omriharel/deej/assets/community-builds/extra/dimitar-schematic.png

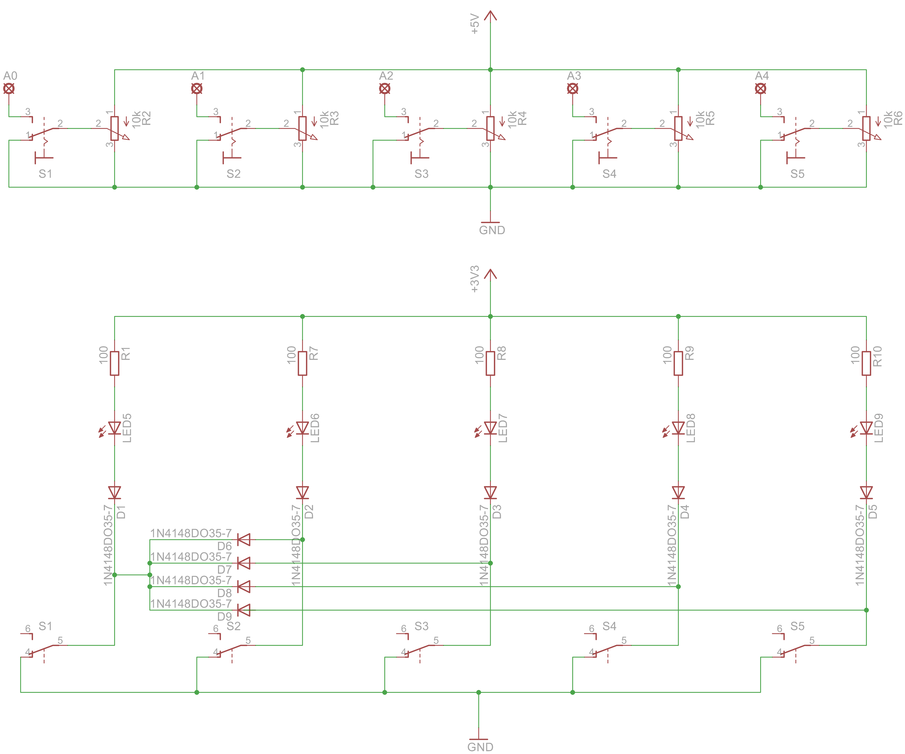
assets/community-builds/extra/dimitar-schematic.png
