omriharel/deej/assets/build-3d.png

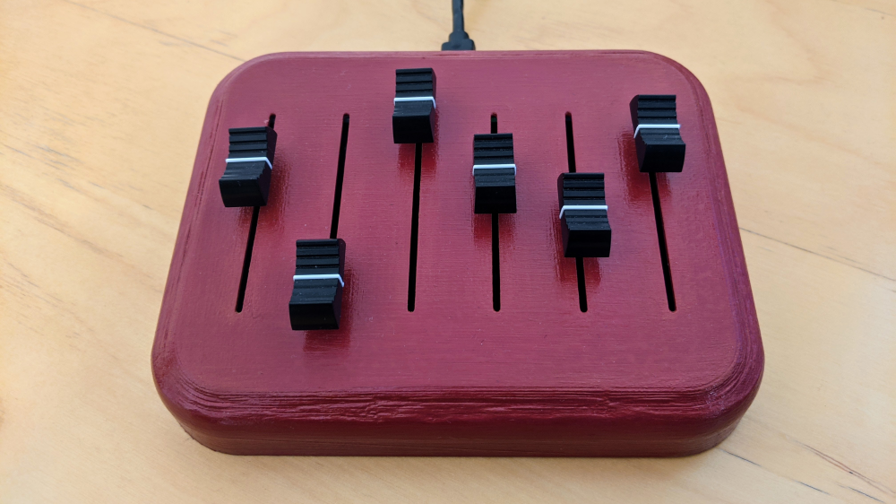
assets/build-3d.png
