omriharel/deej/assets/community-builds/extra/dimitar-schematic.sch

## EAGLE design assets/community-builds/extra/dimitar-schematic.sch (2020-05-23)

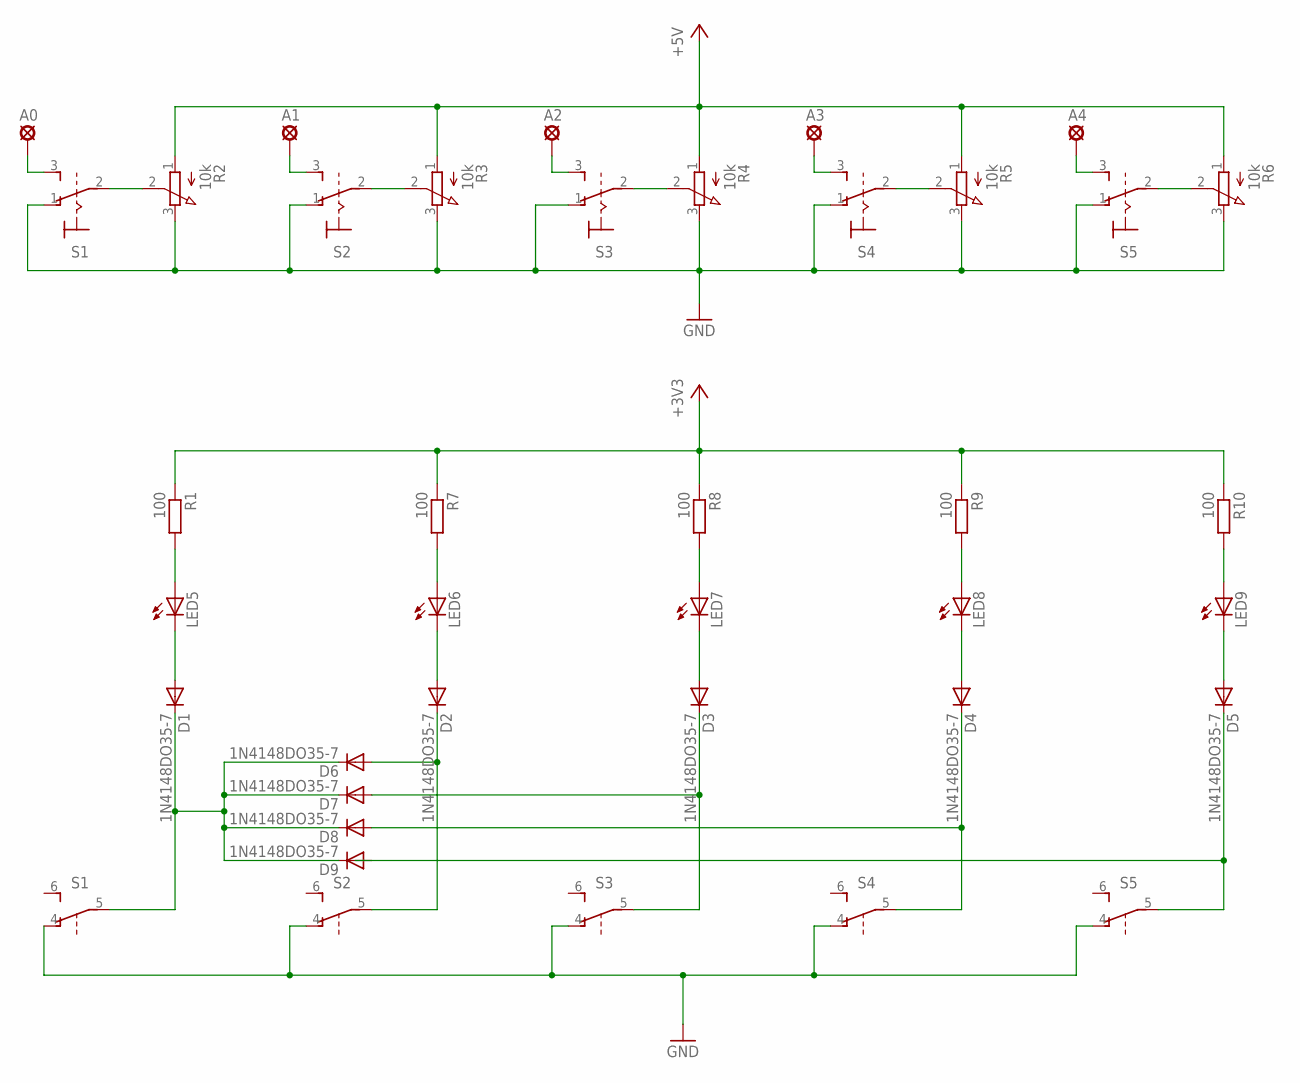
[picture p45: schematic dimitar-schematic.sch]

Parts:
A0, A1, A2, A3, A4: SE14
D1, D2, D3, D4, D5, D6, D7, D8, D9: 1N4148DO35-7; DO35-7
LED5, LED6, LED7, LED8, LED9: LED5MM
R1, R7, R8, R9, R10: 100; 0207/10
R2, R3, R4, R5, R6: 10k; 3RP/1610N
S1, S2, S3, S4, S5: 320-938

Connections:
+3V3: R1.1, R7.1, R8.1, R9.1, R10.1
+5V: R2.1 (A), R3.1 (A), R4.1 (A), R5.1 (A), R6.1 (A)
GND: R2.3 (E), R3.3 (E), R4.3 (E), R5.3 (E), R6.3 (E), S1.1 (O), S1.4 (O), S2.1 (O), S2.4 (O), S3.1 (O), S3.4 (O), S4.1 (O), S4.4 (O), S5.1 (O), S5.4 (O)
unnamed: R2.2 (S), S1.2
unnamed: R3.2 (S), S2.2
unnamed: R4.2 (S), S3.2
unnamed: R5.2 (S), S4.2
unnamed: R6.2 (S), S5.2
unnamed: D1.A, LED5.K (C)
unnamed: A0.MP, S1.3 (S)
unnamed: A1.MP, S2.3 (S)
unnamed: A2.MP, S3.3 (S)
unnamed: A3.MP, S4.3 (S)
unnamed: A4.MP, S5.3 (S)
unnamed: LED5.A, R1.2
unnamed: LED6.A, R7.2
unnamed: LED7.A, R8.2
unnamed: LED8.A, R9.2
unnamed: LED9.A, R10.2
unnamed: D2.A, LED6.K (C)
unnamed: D3.A, LED7.K (C)
unnamed: D4.A, LED8.K (C)
unnamed: D5.A, LED9.K (C)
unnamed: D2.C, D6.A, S2.5
unnamed: D3.C, D7.A, S3.5
unnamed: D4.C, D8.A, S4.5
unnamed: D5.C, S5.5
unnamed: D1.C, D6.C, D7.C, D8.C, D9.C, S1.5
